am009/my-3key-ble-keyboard/photos/2.jpg

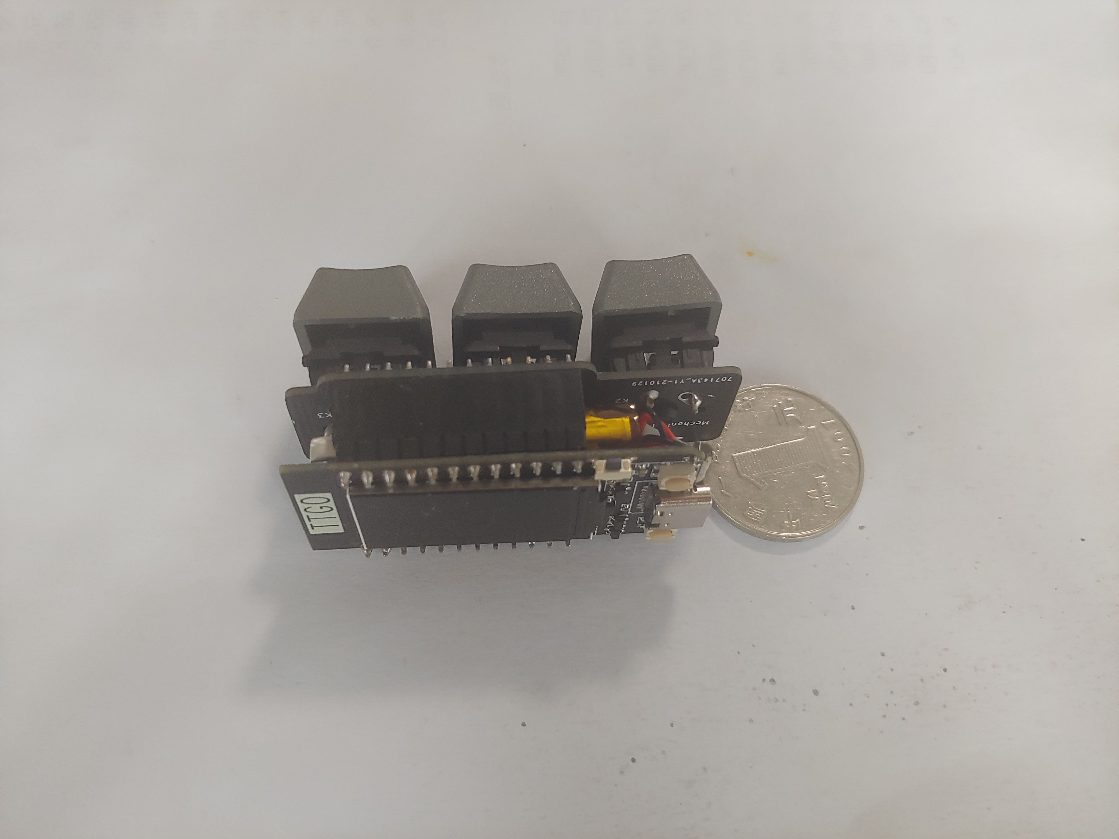
photos/2.jpg
