am009/my-3key-ble-keyboard/photos/3.jpg

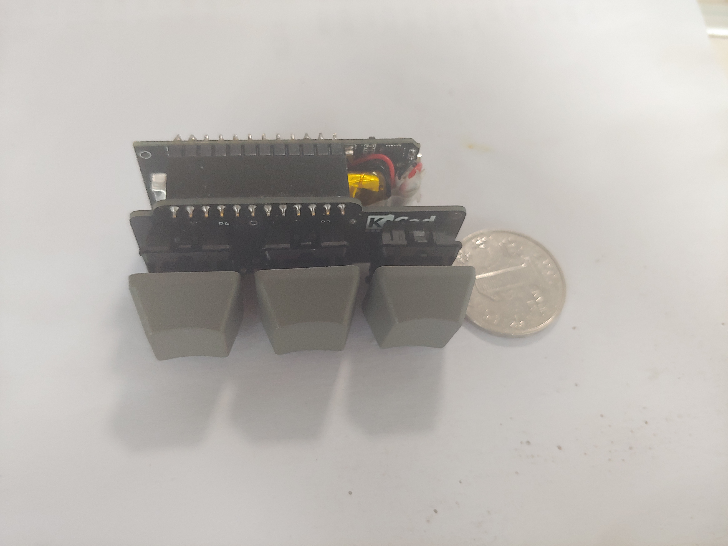
photos/3.jpg
